CrazyRobMiles/PICO-blue-chords/BMSPA_font.h

const uint8_t BMSPA_font[] = {
	8, 8, 0, 32, 126,
	0x00,0x00,0x00,0x00,0x00,0x00,0x00,0x00, //  
	0x00,0x5f,0x00,0x00,0x00,0x00,0x00,0x00, // !
	0x00,0x03,0x00,0x03,0x00,0x00,0x00,0x00, // "
	0x0a,0x1f,0x0a,0x1f,0x0a,0x00,0x00,0x00, // #
	0x24,0x2a,0x2a,0x7f,0x2a,0x2a,0x12,0x00, // $
	0x00,0x47,0x25,0x17,0x08,0x74,0x52,0x71, // %
	0x00,0x36,0x49,0x49,0x49,0x41,0x41,0x38, // &
	0x00,0x03,0x00,0x00,0x00,0x00,0x00,0x00, // '
	0x00,0x3e,0x41,0x00,0x00,0x00,0x00,0x00, // (
	0x41,0x3e,0x00,0x00,0x00,0x00,0x00,0x00, // )
	0x04,0x15,0x0e,0x15,0x04,0x00,0x00,0x00, // *
	0x08,0x08,0x3e,0x08,0x08,0x00,0x00,0x00, // +
	0x00,0xc0,0x00,0x00,0x00,0x00,0x00,0x00, // ,
	0x08,0x08,0x08,0x08,0x08,0x00,0x00,0x00, // -
	0x40,0x00,0x00,0x00,0x00,0x00,0x00,0x00, // .
	0x40,0x20,0x10,0x08,0x04,0x02,0x01,0x00, // /
	0x00,0x3e,0x61,0x51,0x49,0x45,0x43,0x3e, // 0
	0x01,0x01,0x7e,0x00,0x00,0x00,0x00,0x00, // 1
	0x00,0x71,0x49,0x49,0x49,0x49,0x49,0x46, // 2
	0x41,0x49,0x49,0x49,0x49,0x49,0x36,0x00, // 3
	0x00,0x0f,0x10,0x10,0x10,0x10,0x10,0x7f, // 4
	0x00,0x4f,0x49,0x49,0x49,0x49,0x49,0x31, // 5
	0x00,0x3e,0x49,0x49,0x49,0x49,0x49,0x30, // 6
	0x01,0x01,0x01,0x01,0x01,0x01,0x7e,0x00, // 7
	0x00,0x36,0x49,0x49,0x49,0x49,0x49,0x36, // 8
	0x00,0x06,0x49,0x49,0x49,0x49,0x49,0x3e, // 9
	0x14,0x00,0x00,0x00,0x00,0x00,0x00,0x00, // :
	0x40,0x34,0x00,0x00,0x00,0x00,0x00,0x00, // ;
	0x08,0x14,0x22,0x00,0x00,0x00,0x00,0x00, // <
	0x14,0x14,0x14,0x14,0x14,0x00,0x00,0x00, // =
	0x22,0x14,0x08,0x00,0x00,0x00,0x00,0x00, // >
	0x00,0x06,0x01,0x01,0x59,0x09,0x09,0x06, // ?
	0x00,0x3e,0x41,0x5d,0x55,0x5d,0x51,0x5e, // @
	0x00,0x7e,0x01,0x09,0x09,0x09,0x09,0x7e, // A
	0x00,0x7f,0x41,0x49,0x49,0x49,0x49,0x36, // B
	0x00,0x3e,0x41,0x41,0x41,0x41,0x41,0x22, // C
	0x00,0x7f,0x41,0x41,0x41,0x41,0x41,0x3e, // D
	0x00,0x3e,0x49,0x49,0x49,0x49,0x49,0x41, // E
	0x00,0x7e,0x09,0x09,0x09,0x09,0x09,0x01, // F
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
};
