CrazyRobMiles/PICO-blue-chords/acme_5_outlines_font.h

const uint8_t acme_font[] = {
	8, 6, 1, 32, 126,
	0x00,0x00,0x00,0x00,0x00,0x00, //  
	0x7f,0x51,0x7f,0x00,0x00,0x00, // !
	0x0f,0x09,0x0f,0x09,0x0f,0x00, // "
	0x3e,0x6b,0x41,0x6b,0x41,0x6b, // #
	0x7f,0xd1,0x94,0xc5,0x7f,0x00, // $
	0x77,0x4d,0x77,0x59,0x77,0x00, // %
	0x7f,0x49,0x55,0x49,0x6f,0x54, // &
	0x0f,0x09,0x0f,0x00,0x00,0x00, // '
	0x7f,0xc1,0xbe,0xe3,0x00,0x00, // (
	0xe3,0xbe,0xc1,0x7f,0x00,0x00, // )
	0x3e,0x2a,0x77,0x41,0x77,0x2a, // *
	0x1c,0x14,0x77,0x41,0x77,0x14, // +
	0xe0,0xb0,0xd0,0x70,0x00,0x00, // ,
	0x1c,0x14,0x14,0x14,0x1c,0x00, // -
	0x70,0x50,0x70,0x00,0x00,0x00, // .
	0x78,0x4c,0x77,0x19,0x0f,0x00, // /
	0x7f,0x41,0x5d,0x41,0x7f,0x00, // 0
	0x7f,0x41,0x7f,0x00,0x00,0x00, // 1
	0x7f,0x45,0x55,0x51,0x7f,0x00, // 2
	0x7f,0x55,0x55,0x41,0x7f,0x00, // 3
	0x1f,0x11,0x77,0x41,0x7f,0x00, // 4
	0x7f,0x51,0x55,0x45,0x7f,0x00, // 5
	0x7f,0x41,0x55,0x45,0x7f,0x00, // 6
	0x07,0x7d,0x45,0x79,0x0f,0x00, // 7
	0x7f,0x49,0x55,0x49,0x7f,0x00, // 8
	0x7f,0x51,0x55,0x41,0x7f,0x00, // 9
	0x3e,0x2a,0x3e,0x00,0x00,0x00, // :
	0xe0,0xbe,0xda,0x7e,0x00,0x00, // ;
	0x1c,0x36,0x6b,0x5d,0x77,0x00, // <
	0x3e,0x2a,0x2a,0x2a,0x2a,0x3e, // =
	0x77,0x5d,0x6b,0x36,0x1c,0x00, // >
	0x07,0x7d,0x55,0x71,0x1f,0x00, // ?
	0x7f,0x41,0x5d,0x55,0x51,0x7f, // @
	0x7f,0x41,0x75,0x41,0x7f,0x00, // A
	0x7f,0x41,0x55,0x41,0x7f,0x00, // B
	0x7f,0x41,0x5d,0x55,0x77,0x00, // C
	0x7f,0x41,0x5d,0x63,0x3e,0x00, // D
	0x7f,0x41,0x55,0x55,0x7f,0x00, // E
	0x7f,0x41,0x75,0x15,0x1f,0x00, // F
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
};
