CrazyRobMiles/PICO-blue-chords/bubblesstandard_font.h

const uint8_t bubblesstandard_font[] = {
	8, 7, 0, 32, 126,
	0x00,0x00,0x00,0x00,0x00,0x00,0x00, //  
	0xbf,0x00,0x00,0x00,0x00,0x00,0x00, // !
	0x03,0x00,0x03,0x00,0x00,0x00,0x00, // "
	0x24,0x7e,0x24,0x24,0x7e,0x24,0x00, // #
	0x44,0x4a,0xd3,0x22,0x00,0x00,0x00, // $
	0x82,0x60,0x18,0x06,0x21,0x00,0x00, // %
	0x60,0x90,0x8e,0xb9,0x46,0xb0,0x00, // &
	0x03,0x00,0x00,0x00,0x00,0x00,0x00, // '
	0x7e,0x81,0x81,0x00,0x00,0x00,0x00, // (
	0x81,0x81,0x7e,0x00,0x00,0x00,0x00, // )
	0x02,0x0e,0x05,0x0e,0x02,0x00,0x00, // *
	0x10,0x38,0x10,0x00,0x00,0x00,0x00, // +
	0x80,0x00,0x00,0x00,0x00,0x00,0x00, // ,
	0x10,0x10,0x10,0x00,0x00,0x00,0x00, // -
	0x80,0x00,0x00,0x00,0x00,0x00,0x00, // .
	0x80,0x60,0x18,0x06,0x01,0x00,0x00, // /
	0x7e,0x81,0x81,0x7e,0x00,0x00,0x00, // 0
	0x88,0x86,0x7f,0x40,0x00,0x00,0x00, // 1
	0x82,0xc5,0xb1,0x8e,0x40,0x00,0x00, // 2
	0x66,0x81,0x89,0x76,0x00,0x00,0x00, // 3
	0x10,0x18,0x16,0xff,0x08,0x00,0x00, // 4
	0x4e,0x8a,0x8a,0x91,0x61,0x00,0x00, // 5
	0x20,0x78,0x96,0x91,0x60,0x00,0x00, // 6
	0x02,0x02,0xc1,0x39,0x07,0x00,0x00, // 7
	0x76,0x89,0x89,0x76,0x00,0x00,0x00, // 8
	0x06,0x09,0x09,0xfe,0x00,0x00,0x00, // 9
	0x81,0x00,0x00,0x00,0x00,0x00,0x00, // :
	0x81,0x00,0x00,0x00,0x00,0x00,0x00, // ;
	0x10,0x28,0x00,0x00,0x00,0x00,0x00, // <
	0x28,0x28,0x28,0x00,0x00,0x00,0x00, // =
	0x28,0x10,0x00,0x00,0x00,0x00,0x00, // >
	0x06,0x01,0xb1,0x0e,0x00,0x00,0x00, // ?
	0x3c,0x42,0x99,0xa5,0xbd,0xa2,0x1c, // @
	0x50,0x30,0x1c,0x23,0x5c,0xe0,0x00, // A
	0x82,0x7f,0x49,0x36,0x00,0x00,0x00, // B
	0x3c,0x42,0x81,0x89,0x86,0x60,0x00, // C
	0x42,0xff,0xa1,0xa1,0x82,0x7c,0x00, // D
	0x76,0x89,0x81,0x8a,0x70,0x00,0x00, // E
	0x90,0x70,0x1e,0x0a,0x0a,0x01,0x01, // F
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
};
