CrazyRobMiles/PICO-blue-chords/crackers_font.h

const unsigned char crackers_font[] = {
	8, 6, 2, 32, 126,
	0x00,0x00,0x00,0x00,0x00,0x00, //  
	0x5e,0x06,0x06,0x00,0x00,0x00, // !
	0x1e,0x00,0x00,0x1e,0x00,0x00, // "
	0x20,0x7c,0x38,0x38,0x7c,0x08, // #
	0x48,0xfe,0x64,0x64,0x00,0x00, // $
	0x64,0x60,0x60,0x18,0x0c,0x0c, // %
	0x74,0x4a,0x4a,0x7e,0x48,0x00, // &
	0x1e,0x00,0x00,0x00,0x00,0x00, // '
	0x3c,0x7e,0x7e,0x42,0x00,0x00, // (
	0x42,0x7e,0x7e,0x3c,0x00,0x00, // )
	0x04,0x0c,0x04,0x06,0x0c,0x04, // *
	0x10,0x3c,0x3c,0x3c,0x10,0x00, // +
	0x00,0x60,0xe0,0x00,0x00,0x00, // ,
	0x08,0x08,0x08,0x00,0x00,0x00, // -
	0x60,0x60,0x60,0x00,0x00,0x00, // .
	0x60,0x78,0x78,0x1e,0x06,0x00, // /
	0x3c,0x3c,0x7e,0x42,0x7e,0x7e, // 0
	0x04,0x7e,0x7e,0x7e,0x00,0x00, // 1
	0x76,0x7a,0x7e,0x7e,0x4c,0x00, // 2
	0x4a,0x7e,0x7e,0x7c,0x00,0x00, // 3
	0x0e,0x08,0x7e,0x7e,0x7e,0x00, // 4
	0x4e,0x4e,0x4e,0x7a,0x1a,0x00, // 5
	0x3c,0x7e,0x7e,0x4a,0x7a,0x00, // 6
	0x02,0x02,0x0a,0x7e,0x7e,0x7e, // 7
	0x7e,0x7e,0x7e,0x4a,0x7e,0x00, // 8
	0x0c,0x4a,0x7e,0x7e,0x3c,0x00, // 9
	0x66,0x66,0x66,0x00,0x00,0x00, // :
	0x66,0xe6,0x00,0x00,0x00,0x00, // ;
	0x08,0x3c,0x7e,0x7e,0x62,0x00, // <
	0x14,0x14,0x14,0x00,0x00,0x00, // =
	0x62,0x7e,0x7e,0x3c,0x08,0x00, // >
	0x02,0x4a,0x0e,0x0e,0x0c,0x00, // ?
	0x3c,0x7e,0x7e,0x4a,0x72,0x30, // @
	0x7a,0x4a,0x7e,0x7e,0x7c,0x00, // A
	0x7e,0x7e,0x7e,0x4a,0x24,0x00, // B
	0x3c,0x7e,0x7e,0x7e,0x46,0x00, // C
	0x7e,0x7e,0x7e,0x62,0x3c,0x00, // D
	0x7e,0x7e,0x7e,0x4a,0x00,0x00, // E
	0x7e,0x7e,0x7e,0x0a,0x00,0x00, // F
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
};
