CrazyRobMiles/PICO-blue-chords/messages.h

void init_messages();

void display_message(const char *s);

void display_bluetooth_status(const char *s);

void display_shift_status(const char *s);

void add_character_to_message(char ch);

void clear_message();
