CrazyRobMiles/PICO-blue-chords/picow_bt_example_common.h

/**
 * 
 * By Rob Miles 2023
 * 
 * Based on examples:
 * 
 * Copyright (c) 2022 Raspberry Pi (Trading) Ltd.
 *
 * SPDX-License-Identifier: BSD-3-Clause
 */

/*
 * \brief Initialise BTstack example with cyw43
 *
 * \return 0 if ok
 */
int picow_bt_example_init(void);

/*
 * \brief Run the BTstack example
 *
 */
void pico_blue_chords_main(void);
